UCSIG/attiny85_time_switch/docu/Prototyp.jpg

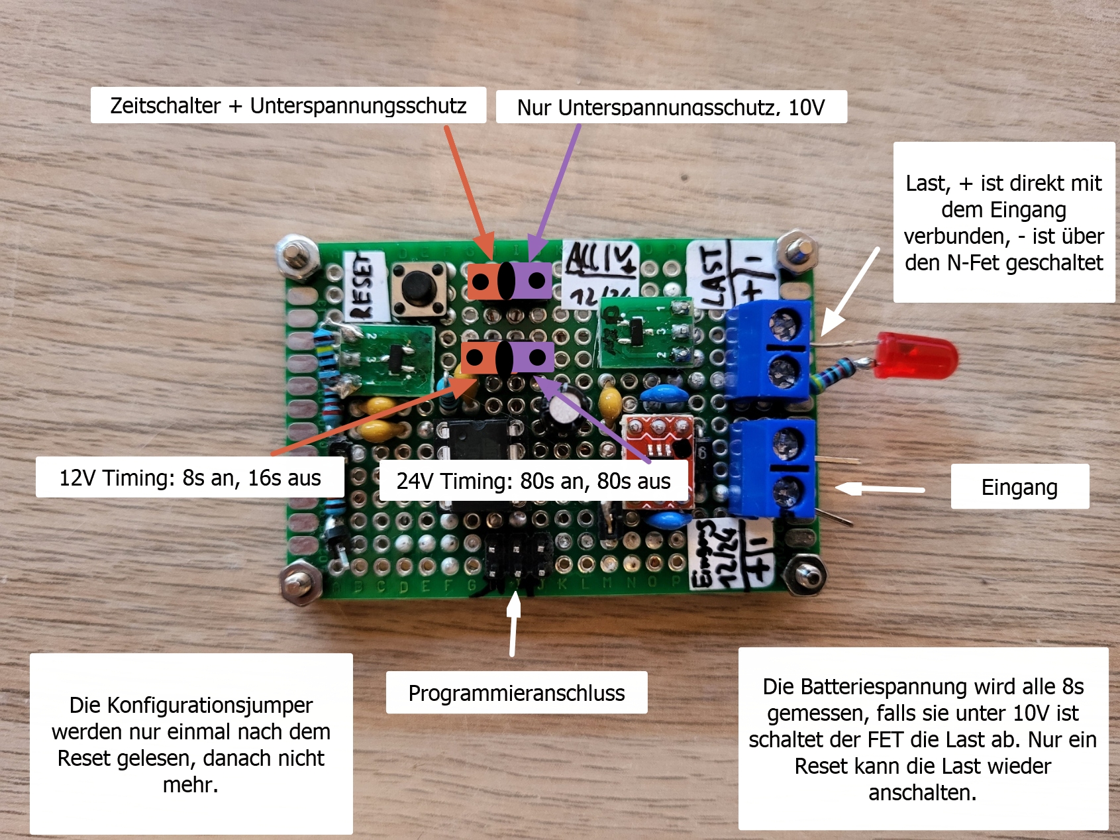
docu/Prototyp.jpg
